flavio-fernandes/lora-ben/lora.py

# SPDX-FileCopyrightText: 2021 ladyada for Adafruit Industries
# SPDX-License-Identifier: MIT

# Simple demo of sending and recieving data with the RFM95 LoRa radio.
# Author: Tony DiCola
import board
import busio
import digitalio
import adafruit_rfm9x

# Define radio parameters.
RADIO_FREQ_MHZ = 915.0  # Frequency of the radio in Mhz. Must match your
# module! Can be a value like 915.0, 433.0, etc.

CS = digitalio.DigitalInOut(board.D10)
RESET = digitalio.DigitalInOut(board.D11)

# Initialize SPI bus.
spi = busio.SPI(board.SCK, MOSI=board.MOSI, MISO=board.MISO)

# Initialze RFM radio
rfm9x = adafruit_rfm9x.RFM9x(spi, CS, RESET, RADIO_FREQ_MHZ)

# Note that the radio is configured in LoRa mode so you can't control sync
# word, encryption, frequency deviation, or other settings!

# You can however adjust the transmit power (in dB).  The default is 13 dB but
# high power radios like the RFM95 can go up to 23 dB:
rfm9x.tx_power = 23

# This setting makes source and destination more specific.
rfm9x.node = 1
# rfm9x.destination = 8


def send_report(sequence, battery, temperature, distance):
    msg = bytes(
        f"id:{sequence}, batt:{battery} v, temp:{temperature} F, dist:{distance} mm",
        "utf-8",
    )
    msg_len = len(msg)
    print(f"len:{msg_len} msg:{msg}")
    rfm9x.send(msg)
    return msg_len < 256
